Susssiest/Card-Pulse/Card Pulse.sch

## KiCad design Card Pulse.sch (2026-09-08)

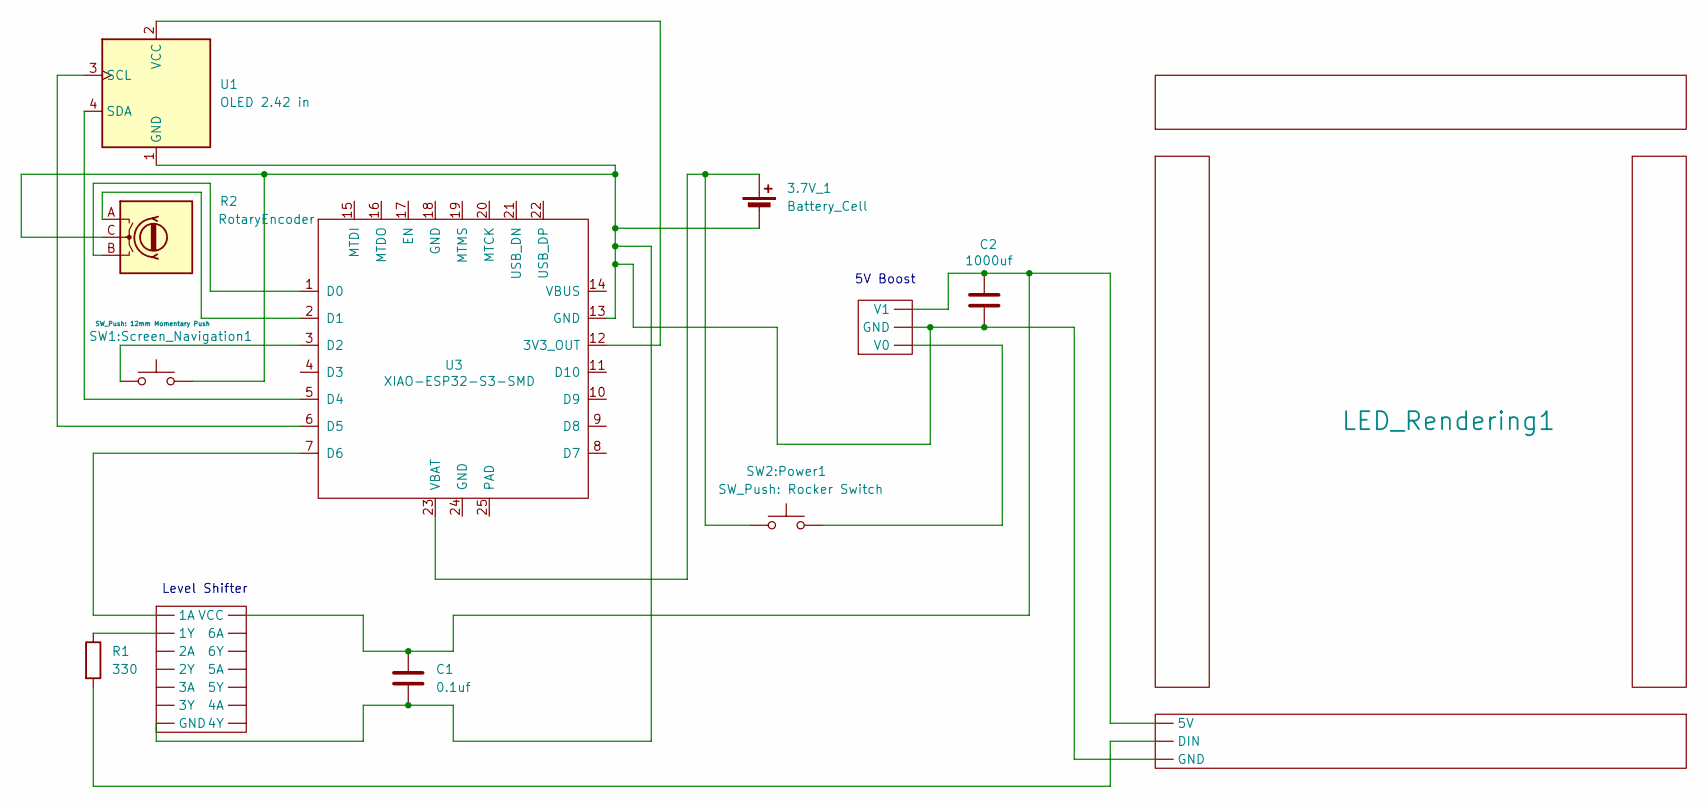
[picture p16: schematic Card Pulse.sch]

Parts:
3.7V_1: Battery_Cell
C1: 0.1uf
C2: 1000uf
LED_Rendering1: (no value)
R1: 330
R2: RotaryEncoder
SW1:Screen_Navigation1: SW_Push: 12mm Momentary Push
SW2:Power1: SW_Push: Rocker Switch
U1: OLED 2.42 in; ER_OLEDM0.91_1x-I2C
U2, U4: (no value)
U3: XIAO-ESP32-S3-SMD

Connections:
unnamed: 3.7V_1.1 (+), SW2:Power1.1, U3.23 (VBAT)
unnamed: 3.7V_1.2 (-), C1.2, C2.2, LED_Rendering1., R2.C, SW1:Screen_Navigation1.2, U1.1 (GND), U2., U3.13 (GND), U4.
unnamed: C1.1, C2.1, LED_Rendering1., U2., U4.
unnamed: LED_Rendering1., R1.2
unnamed: R1.1, U2.
unnamed: R2.A, U3.2 (D1)
unnamed: R2.B, U3.1 (D0)
unnamed: SW1:Screen_Navigation1.1, U3.3 (D2)
unnamed: SW2:Power1.2, U4.
unnamed: U1.2 (VCC), U3.12 (3V3_OUT)
unnamed: U1.3 (SCL), U3.6 (D5)
unnamed: U1.4 (SDA), U3.5 (D4)
unnamed: U2., U3.7 (D6)

Notes on the sheet:
5V Boost
Level Shifter
